Hasatio/esp32DevKitS/Rev2/panelization/Gerbers/panelization-F_Paste.pdf

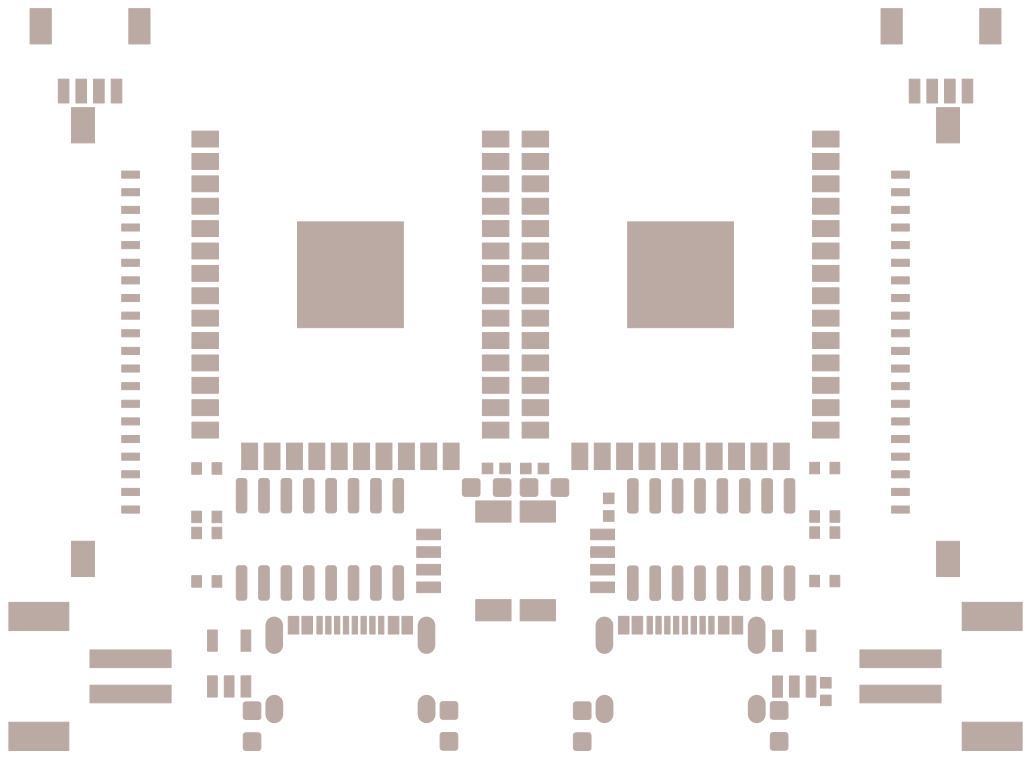
[picture p13: page 1]
