Hasatio/esp32DevKitS/Rev2/panelization/Gerbers/panelization-F_Silkscreen.pdf

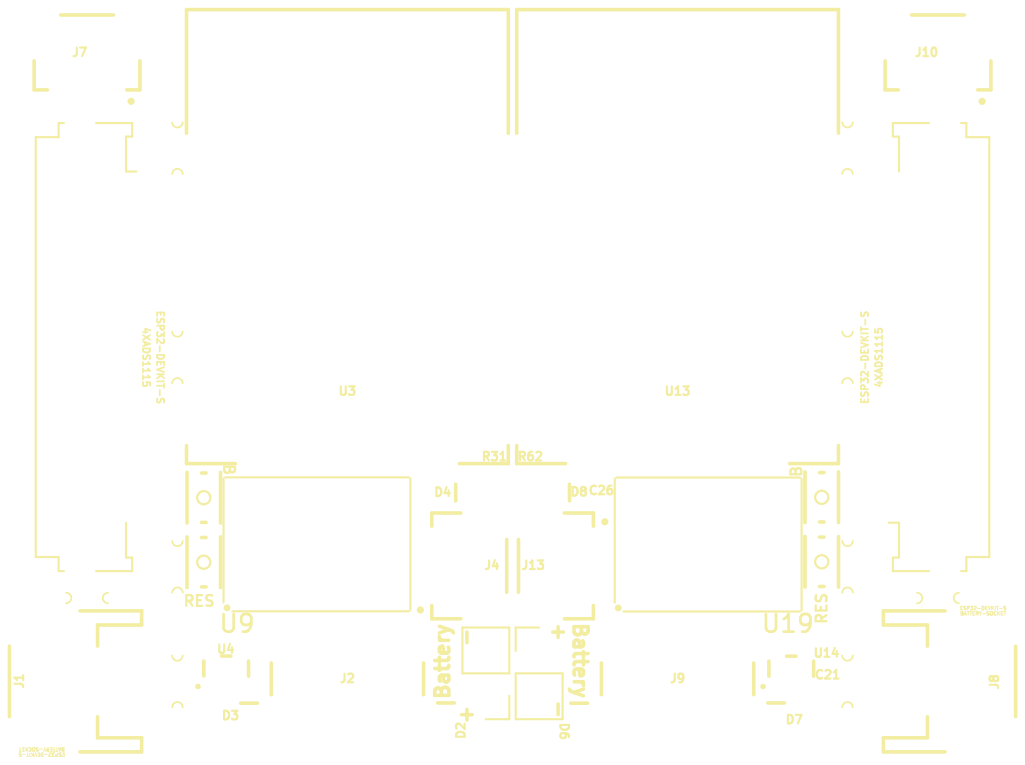
[picture p14: page 1]
